diggit/wthr_station/photo/P1050688.jpg

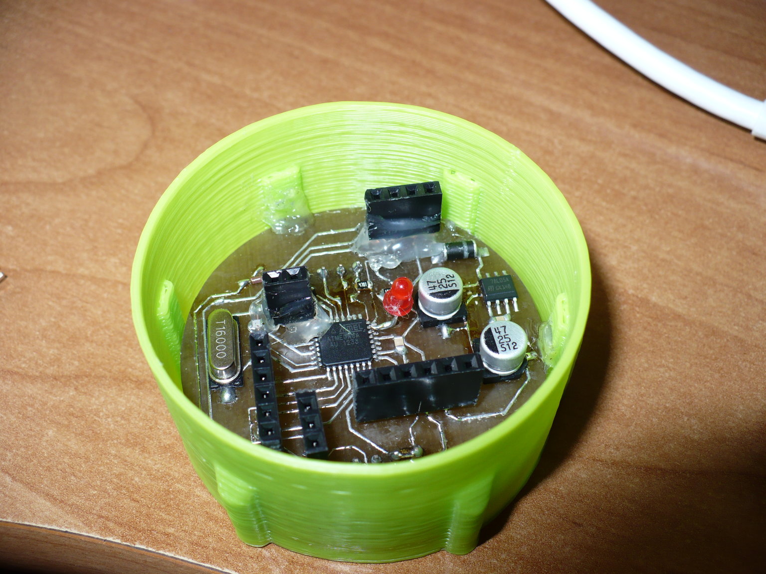
photo/P1050688.jpg
