diggit/wthr_station/photo/P1050690.jpg

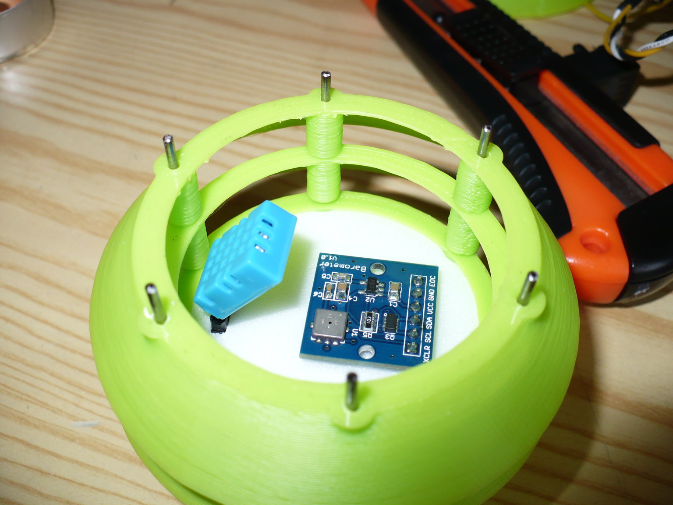
photo/P1050690.jpg
