diggit/wthr_station/photo/P1050697.jpg

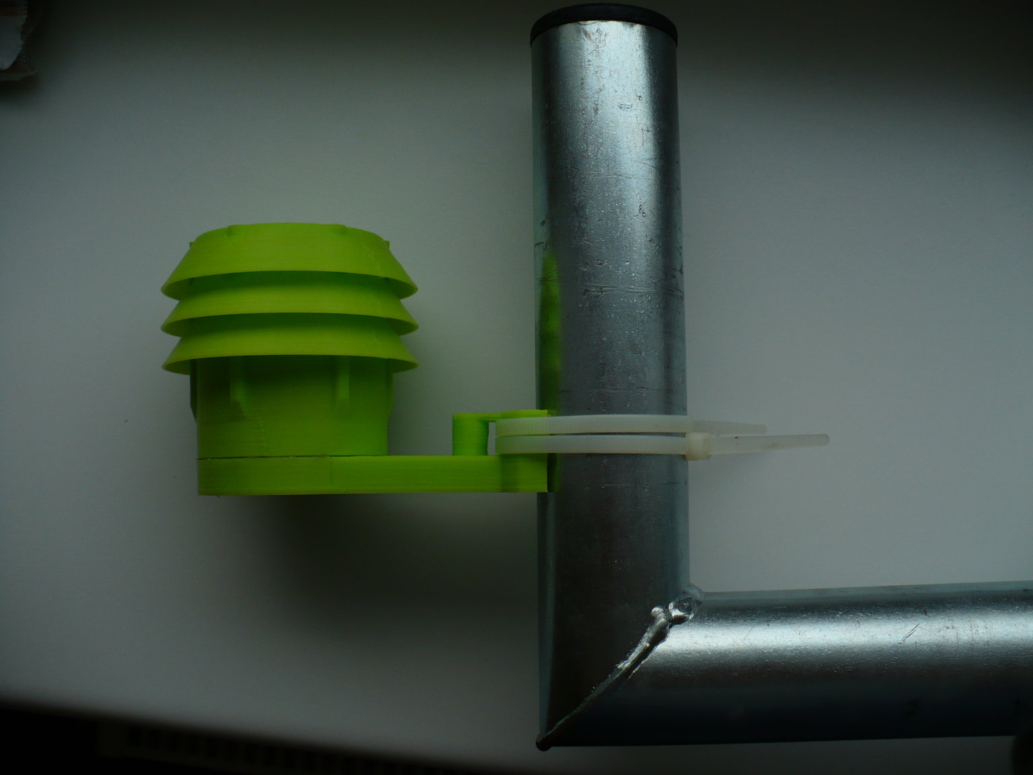
photo/P1050697.jpg
