diggit/wthr_station/photo/P1050699.jpg

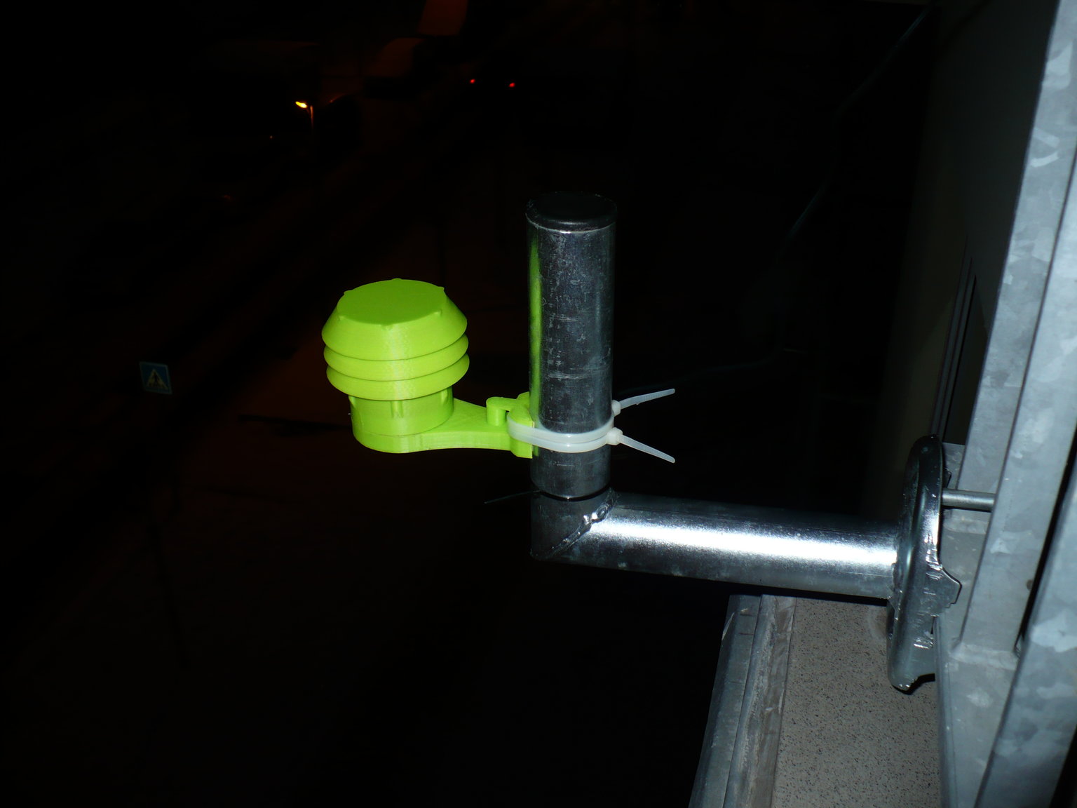
photo/P1050699.jpg
