diggit/wthr_station/photo/P1050765.jpg

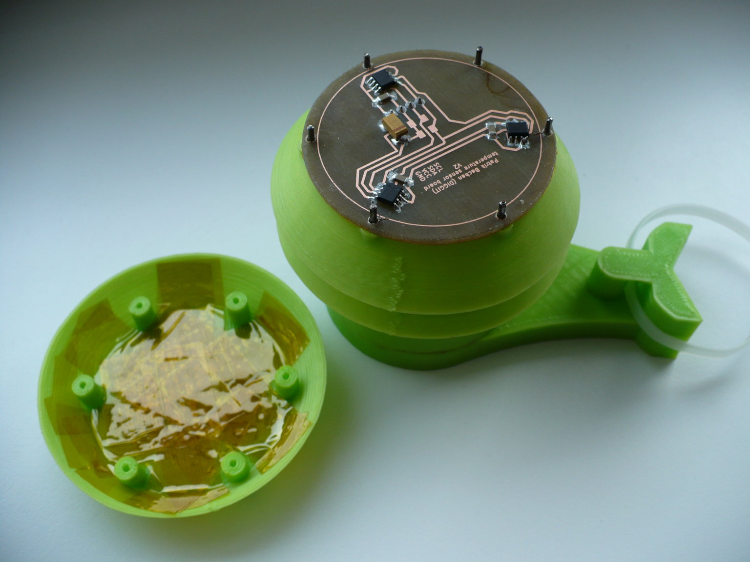
photo/P1050765.jpg
