diggit/wthr_station/web_app/charts/humi-lowres.png

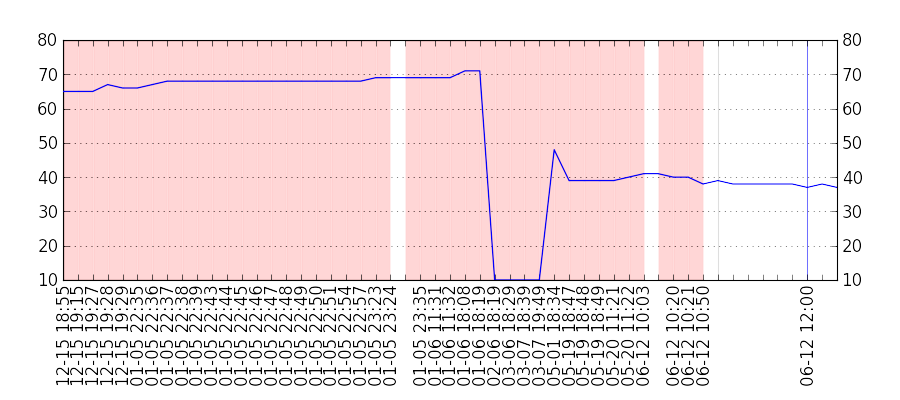
web_app/charts/humi-lowres.png
