diggit/wthr_station/web_app/charts/humi.png

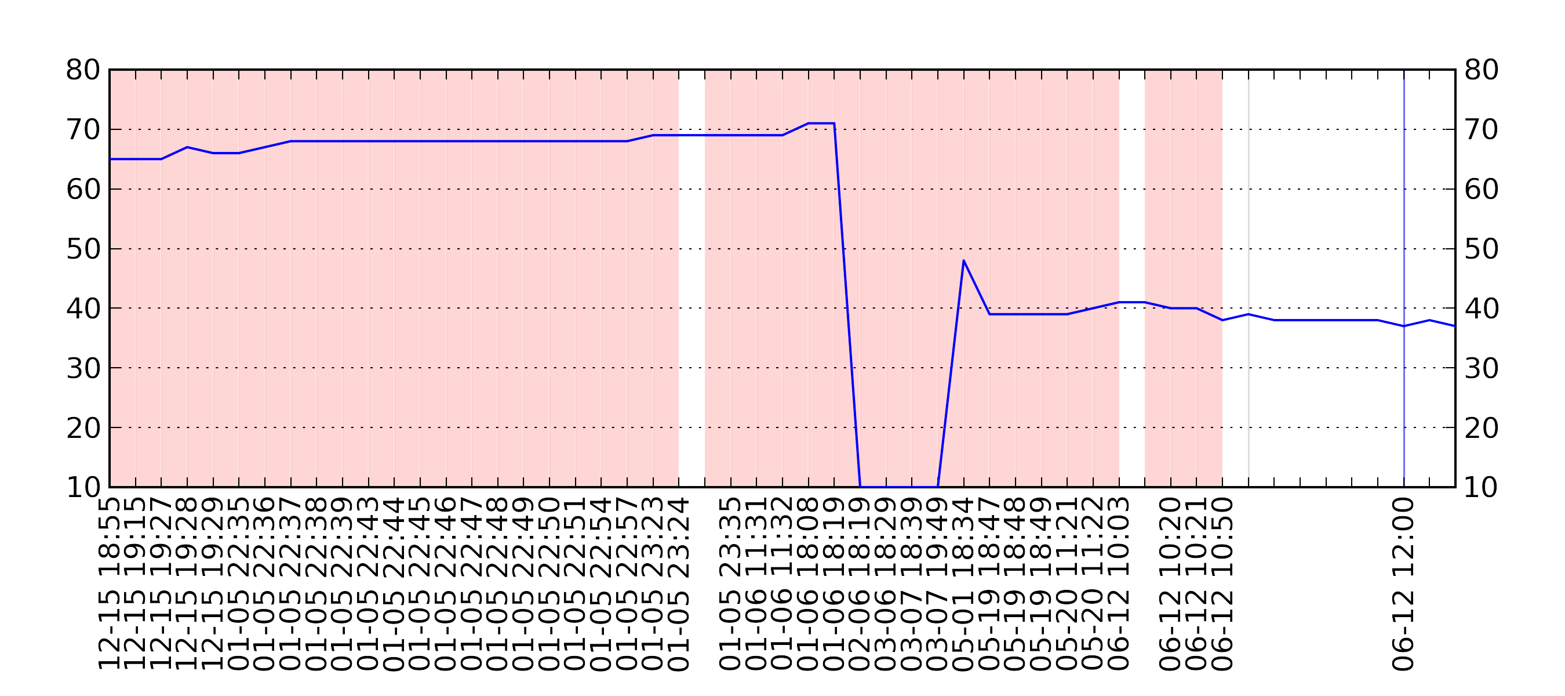
web_app/charts/humi.png
