diggit/wthr_station/web_app/charts/pres-lowres.png

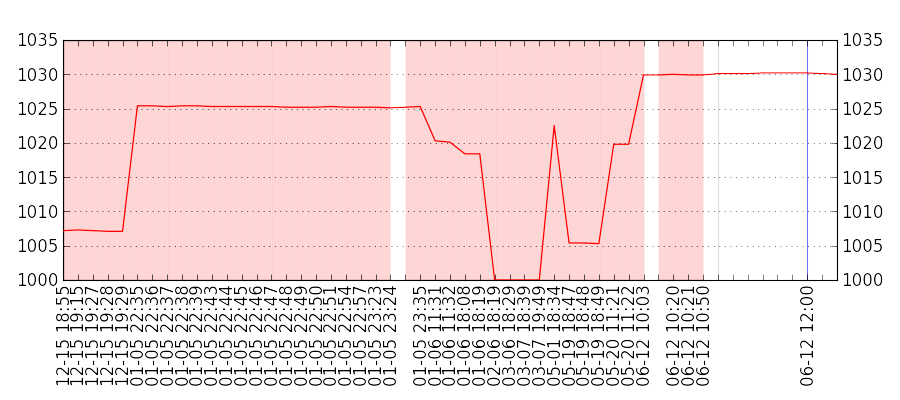
web_app/charts/pres-lowres.png
