diggit/wthr_station/web_app/charts/temp.png

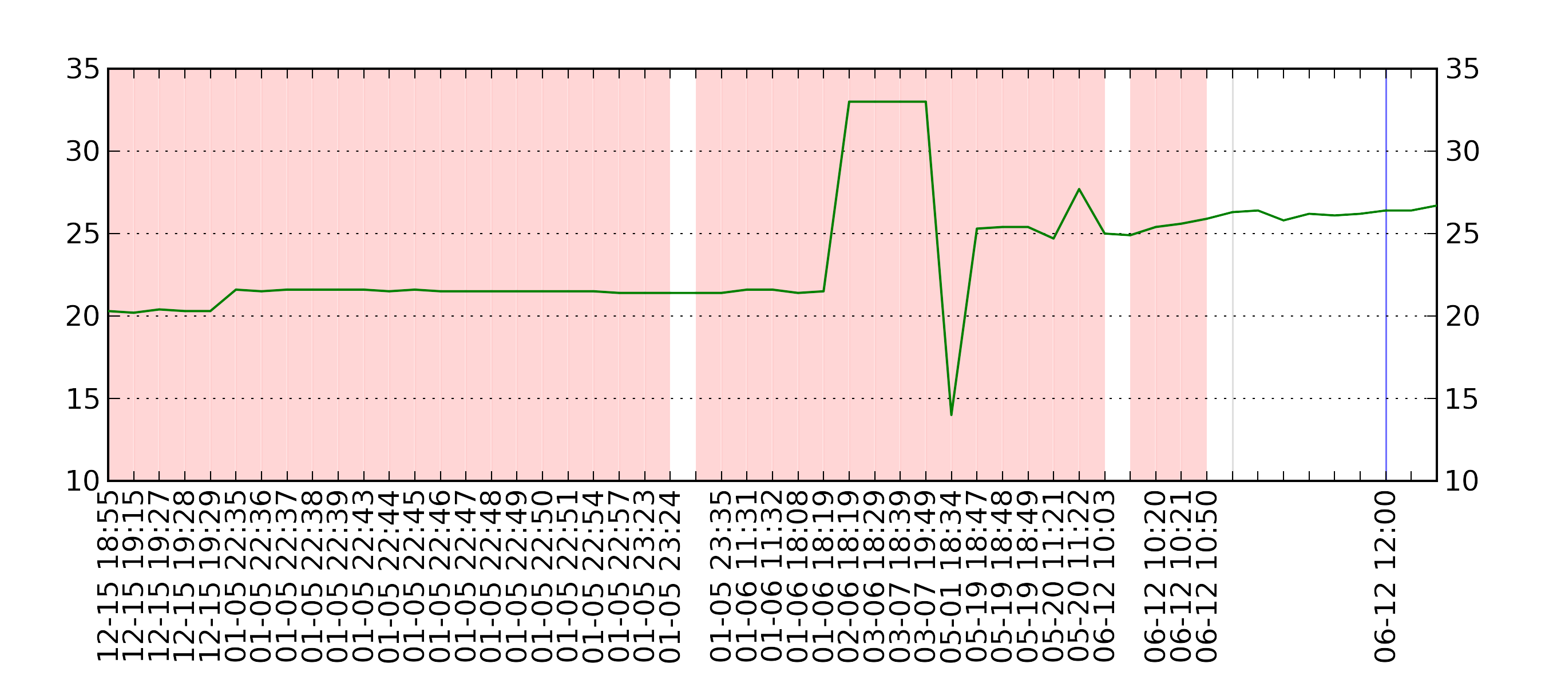
web_app/charts/temp.png
