diggit/wthr_station/web_app/photo/img1.png

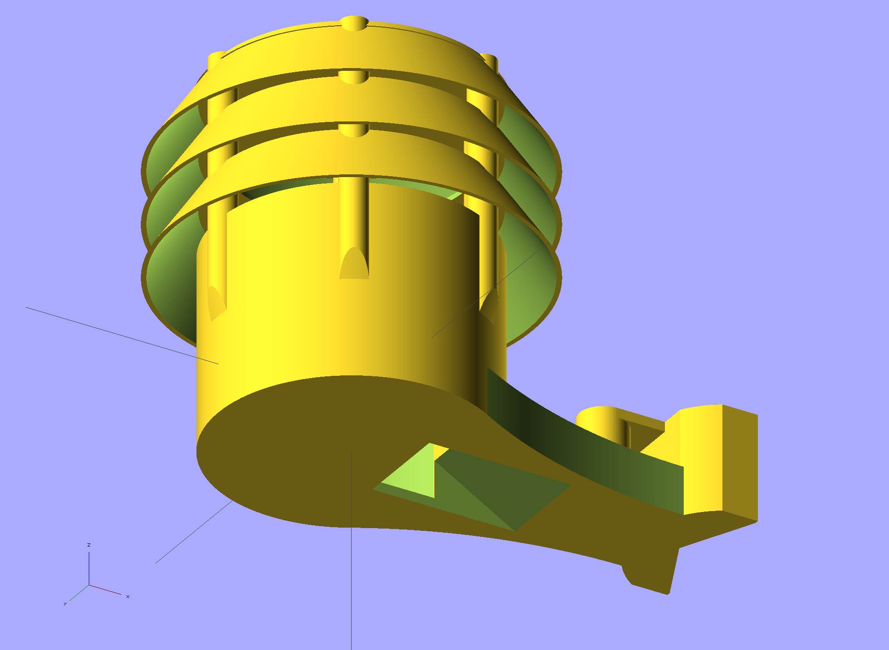
web_app/photo/img1.png
