diggit/wthr_station/web_app/photo/img2.jpg

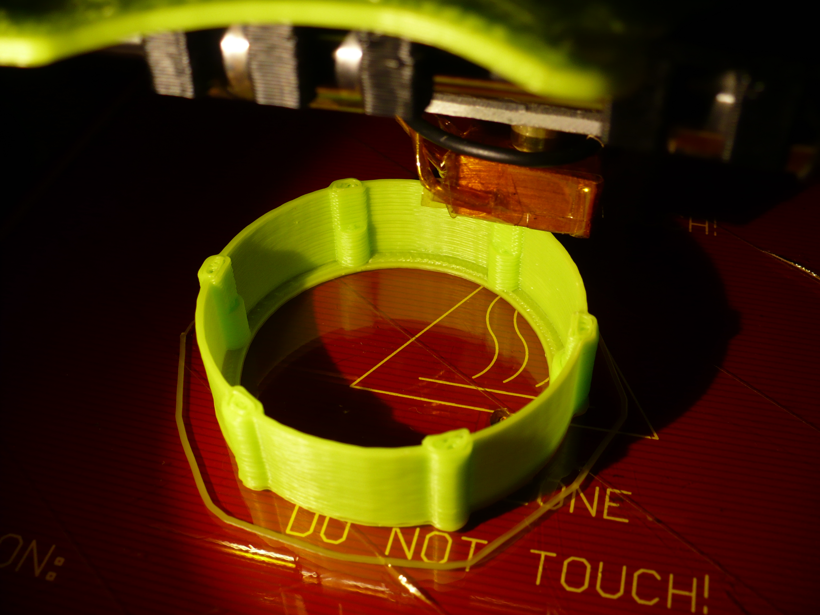
web_app/photo/img2.jpg
