diggit/wthr_station/web_app/photo/img6.jpg

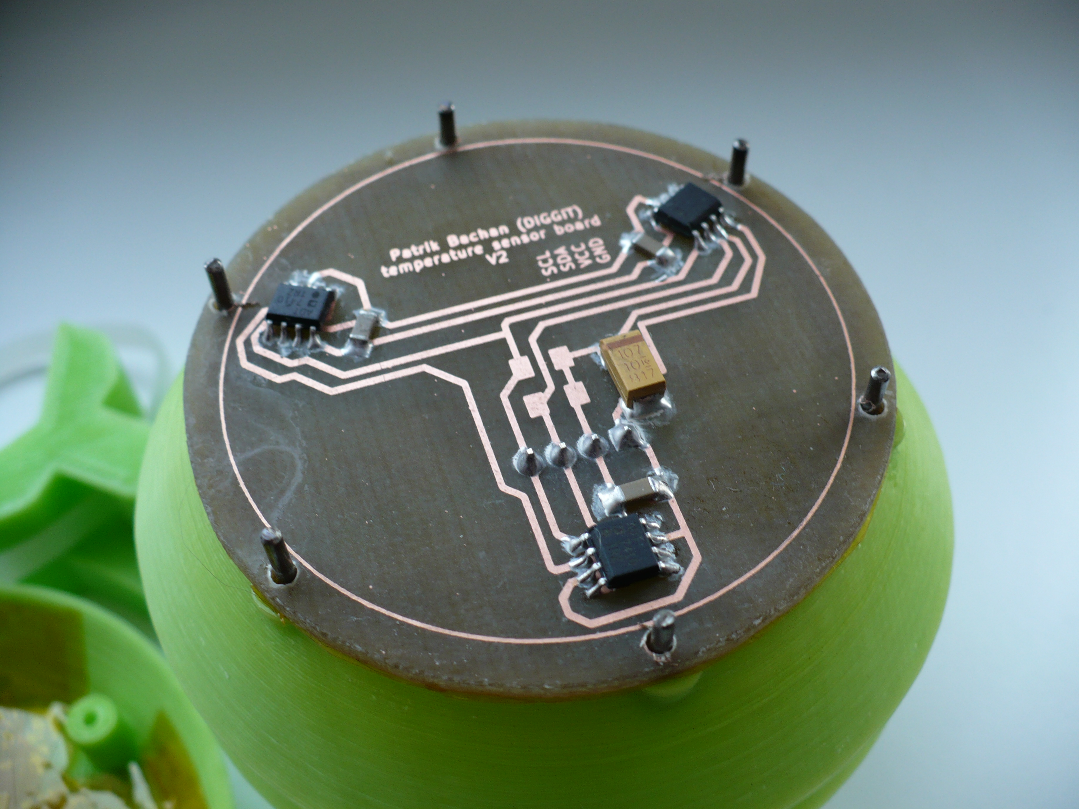
web_app/photo/img6.jpg
