diggit/wthr_station/web_app/photo/img7.jpg

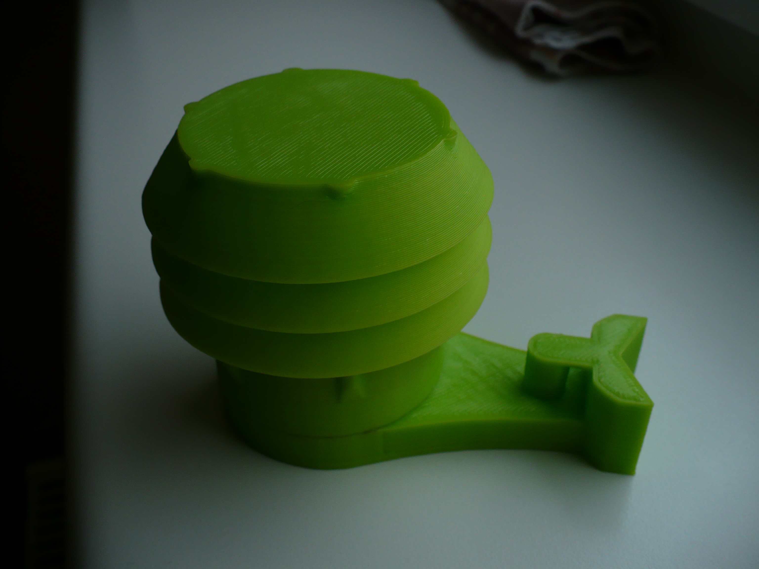
web_app/photo/img7.jpg
