diggit/wthr_station/web_app/photo/img8.jpg

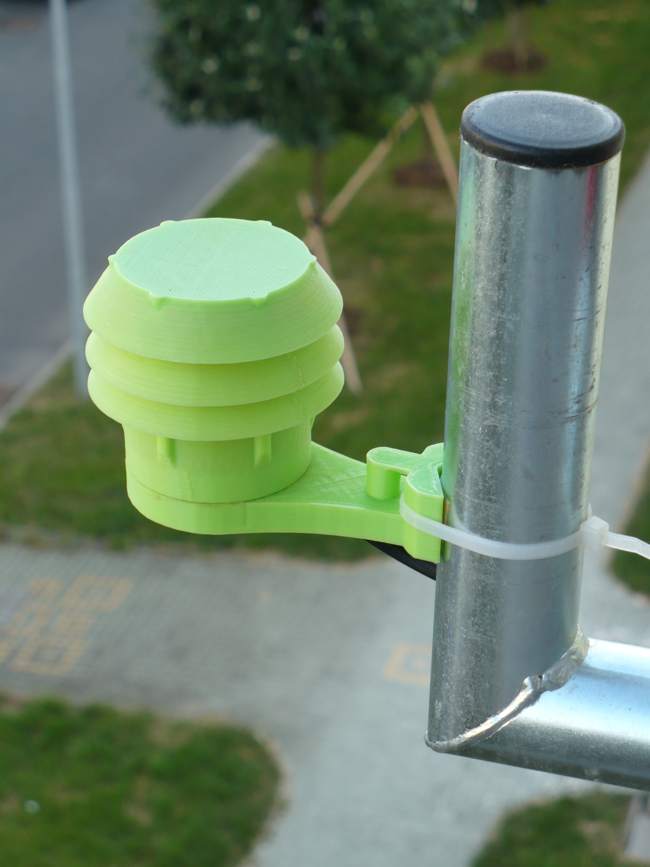
web_app/photo/img8.jpg
