diggit/wthr_station/web_app/photo/img9.jpg

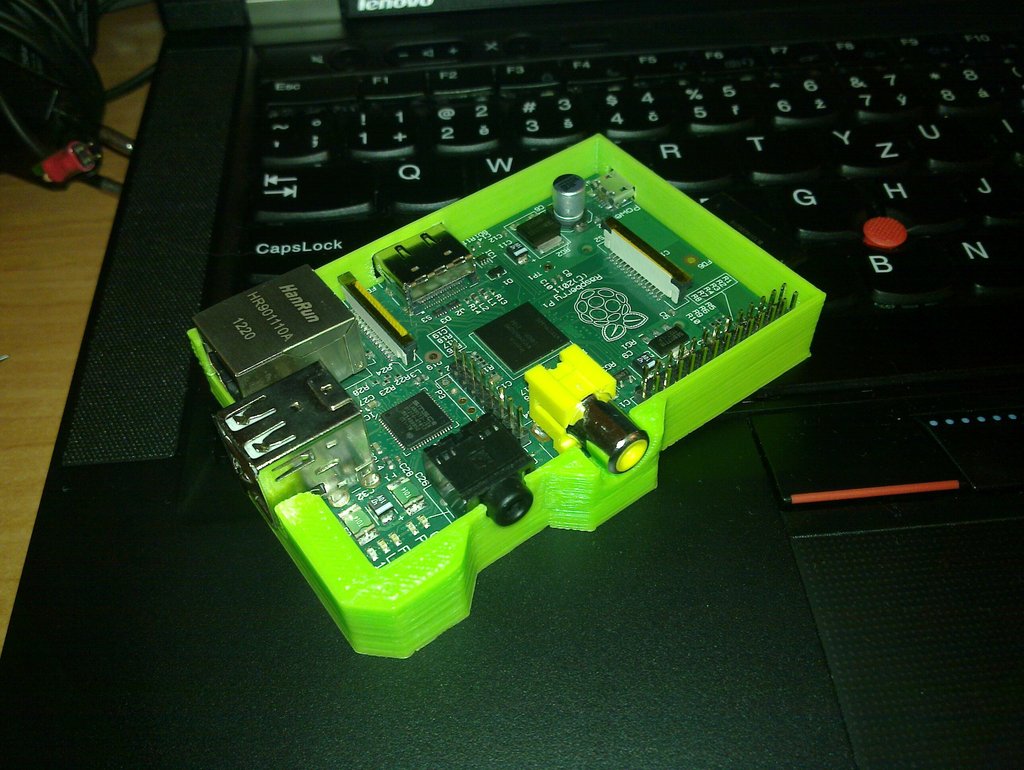
web_app/photo/img9.jpg
