diggit/wthr_station/multi_sens/uart.c

// Copyright (C) 2014  xorly

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

#include "uart.h"


//functions available for receiving
#ifdef UART_RX
	unsigned char uart_getc( void )
	{
		while ( !(UCSRA & (1<<RXC)) )
			NOP;
		return UDR;
	}

	//flush input buffer
	void uart_flush()
	{
		UCSRB &= ~(1<<RXEN);
		UCSRB |= (1<<RXEN);
	}
#endif

//functions available for transmitting
#ifdef UART_TX
	// send char
	void uart_putc(char data)
	{
		while ( !( UCSRA & (1<<UDRE)) )
			NOP;
		UDR = data;
	}

	void uart_nl()
	{
		uart_putc('\n');
	}

	//send string, (BTW string is array of chars, if you don't know...)
	

	void uart_puts_endchar(char *str,char endchar)
	{
		for(; *str != '\0'; str++)// while character on given address is not EQ \0, send it, increase address and iterate!
		{
			uart_putc(*str);//send character which is located on address called str here, *str gives value (char) stored there
		}
		if(endchar)
			uart_putc(endchar);
	}

	void uart_print(char *str)//accepts address on array beginning
	{
		uart_puts_endchar( str,0);
	}
	void uart_println(char *str)//accepts address on array beginning
	{
		uart_puts_endchar( str,'\n');
	}

#endif

void uart_init(void)
{
	
	//set prescaler
	UBRRL = (uint8_t)ubrr_val;
	UBRRH = (uint8_t)ubrr_val>>8;

	//enable RX nad TX, conditionaly

#ifdef UART_TX
	UCSRB |= (1<<TXEN);
#endif

#ifdef UART_RX
	UCSRB |= (1<<RXEN);
	#ifdef UART_RX_INT
		UCSRB |= (1<<RXCIE); //enable RX interrupt
	#endif
#endif

	//set frame format 8data bits, 1 stop bit, no parity
	UCSRC |= (1<<URSEL) | (1<<UCSZ0) | (1<<UCSZ1); //but it is default...
	//URSEL MUST! by written when we really want to write into UCSRC and no into UBRRH (they are shared, URSEL selects in 1 UCSRC)
}
